valerionew/colors-of-italy/docs/img/_1011707 - 250 x 250.jpg

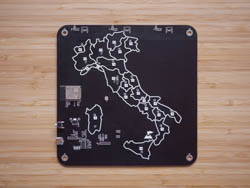
docs/img/_1011707 - 250 x 250.jpg
